pepaslabs/isothermal/ltspice/100k/divider/-3C-59C-33k-100k-100k-10k.png

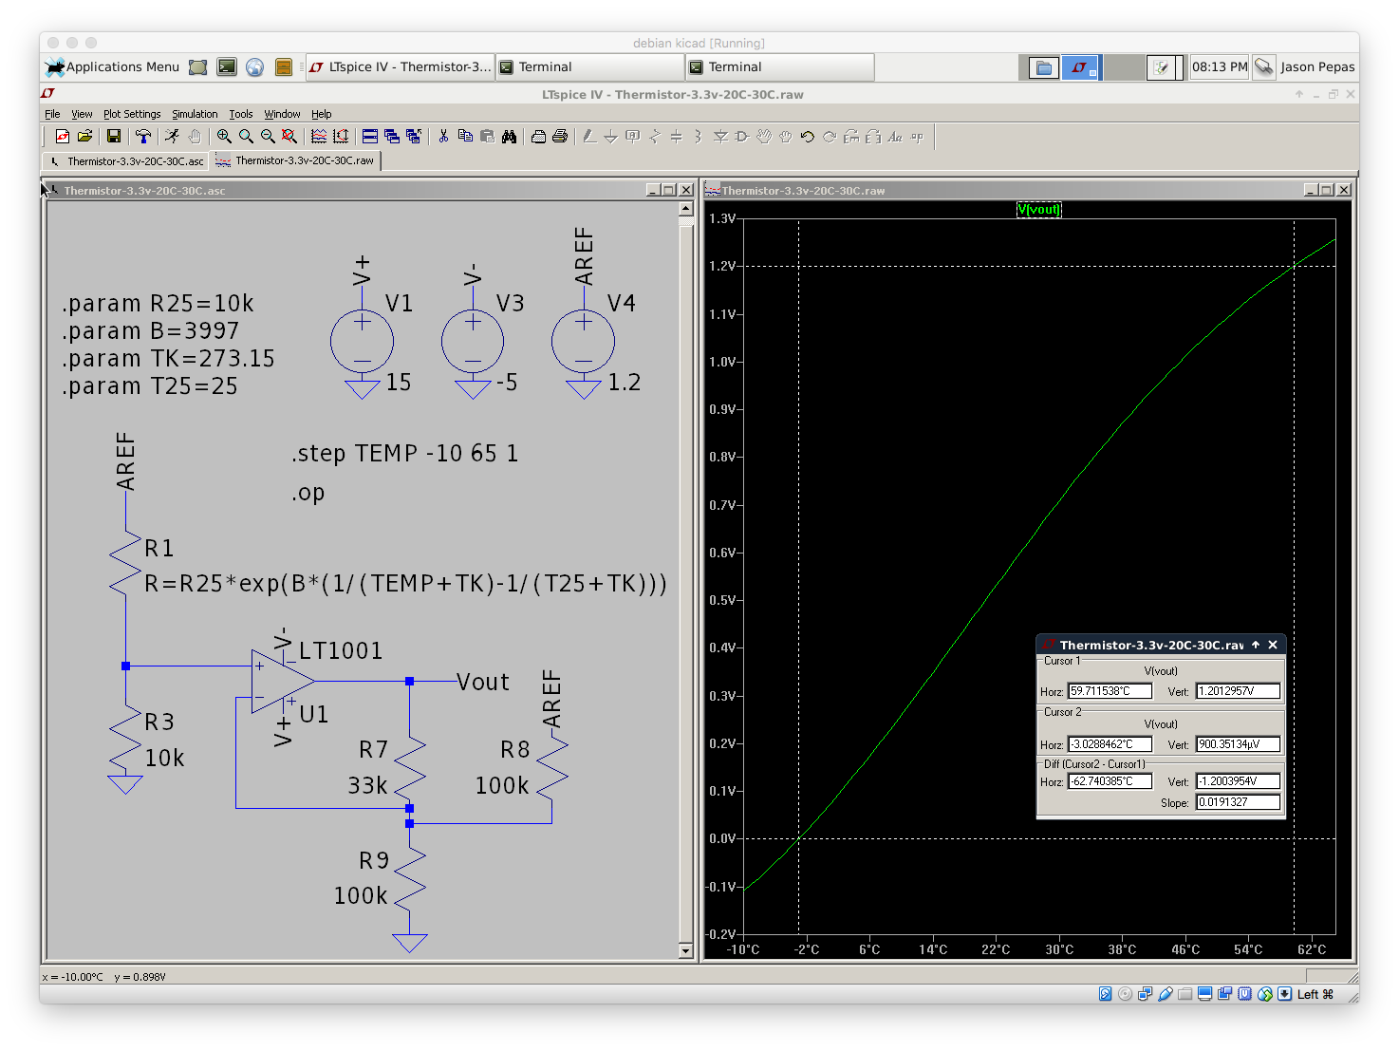
ltspice/100k/divider/-3C-59C-33k-100k-100k-10k.png
