pepaslabs/isothermal/ltspice/Thermistor-3.3v-10C-45C.asc

R1: res; R=R25*exp(B*(1/(TEMP+TK)-1/(T25+TK)))
R3: res; 6.81k
R7: res; 75k
R8: res; 100k
R9: res; 59k
U1: LT1001
V1: voltage; 15
V3: voltage; -15
V4: voltage; 3.3
Named nets: 0, V+, V-, 3v3, Vout
.param R25=10k
.param B=3892
.param TK=273.15
.param T25=25
.step TEMP 5 50 1
.op
