pepaslabs/isothermal/ltspice/Thermistor-3.3v-20C-30C.asc

R1: res; R=R25*exp(B*(1/(TEMP+TK)-1/(T25+TK)))
R3: res; 10k
R7: res; 120k
R8: res; 33k
R9: res; 33k
U1: LT1001
V1: voltage; 30
V3: voltage; -30
V4: voltage; 3.3
Named nets: 0, V+, V-, 3v3, Vout
.param R25=10k
.param B=3997
.param TK=273.15
.param T25=25
.step TEMP 19 31 1
.op
